Anycircle11139s/Stardance-Hackpad/images/pcb-bottom-render.png

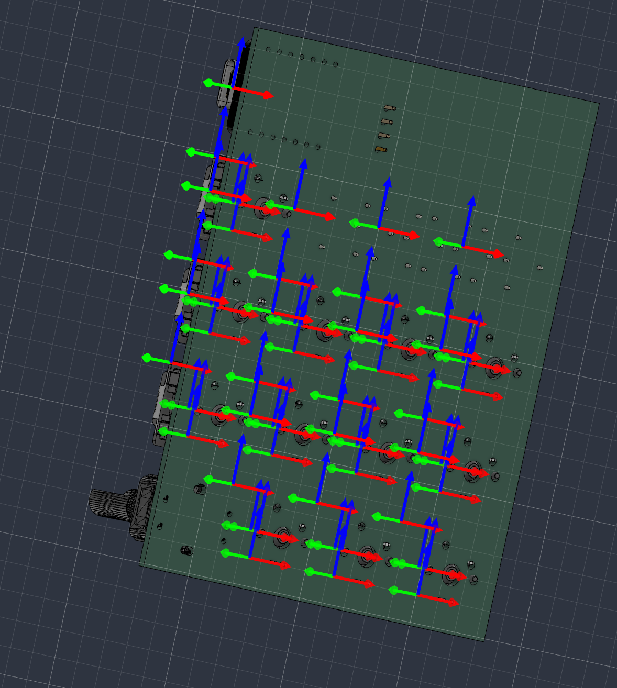
images/pcb-bottom-render.png
