Anycircle11139s/Stardance-Hackpad/images/pcb-top-render.png

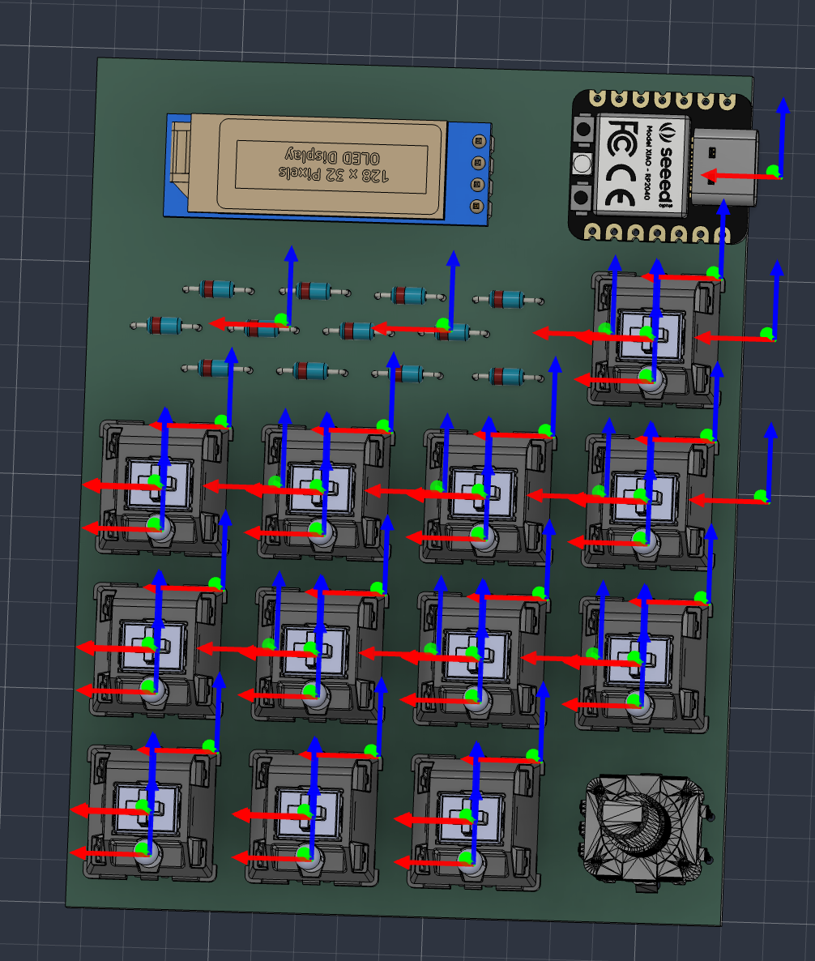
images/pcb-top-render.png
