Anycircle11139s/Stardance-Hackpad/images/top-plate.png

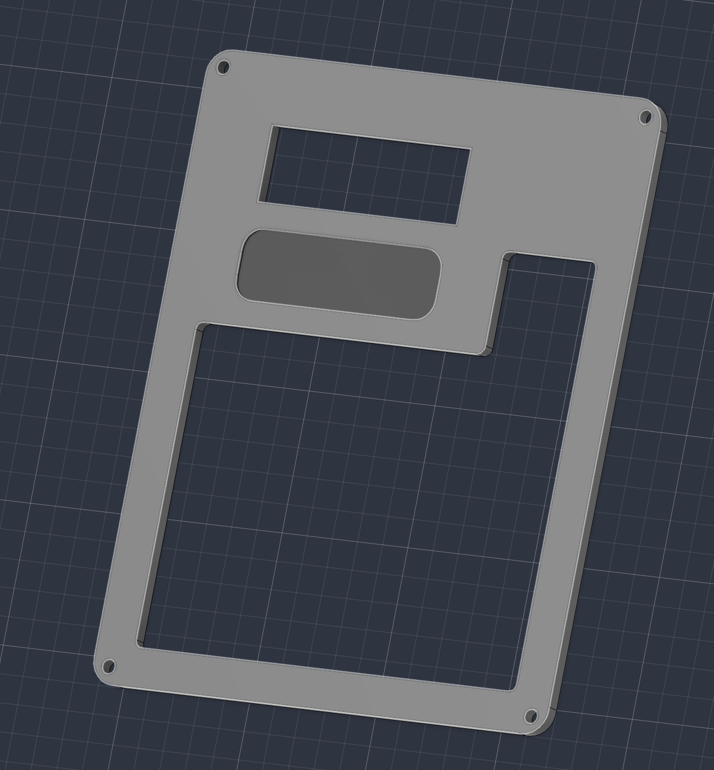
images/top-plate.png
